agekoda/phantomware/images/3d 4.png

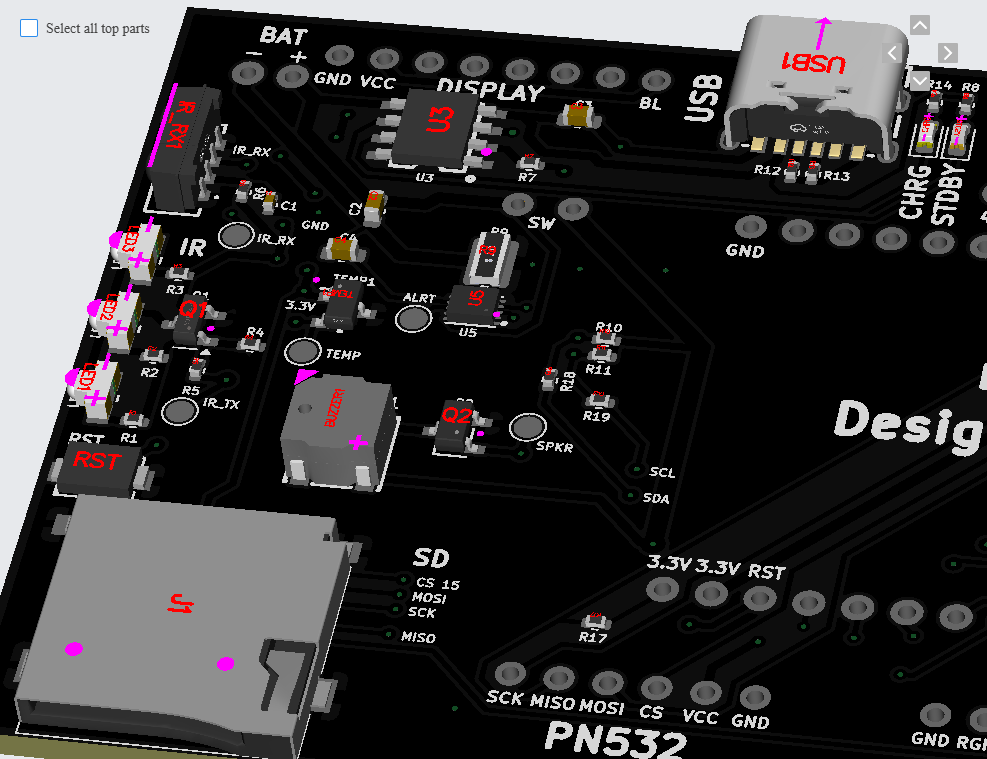
images/3d 4.png
